LucaPaccard/INSA_ProjetCapteur/Application bluetooth/Face_avant_application.jpg

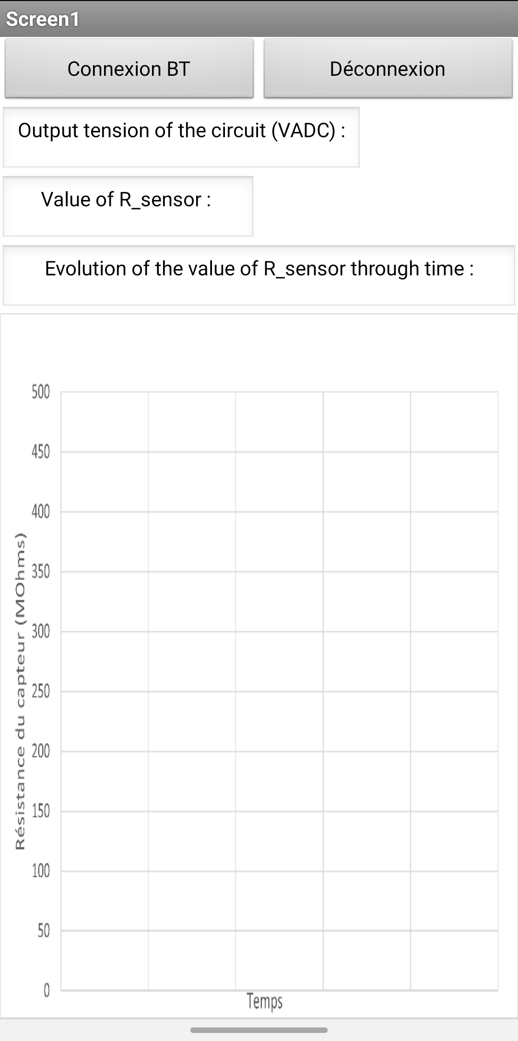
Application bluetooth/Face_avant_application.jpg
